seandepagnier/ais_monitor/src/nmea.py

#   Copyright (C) 2024 Sean D'Epagnier
#
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
# nmea uses a simple xor checksum
def nmea_cksum(msg):
    value = 0
    for c in msg: # skip over the $ at the begining of the sentence
        value ^= ord(c)
    return value & 255

def check_nmea_cksum(line):
    cksplit = line.split('*')
    try:
        computed = nmea_cksum(cksplit[0][1:])
        lineck = int(cksplit[1], 16)
        if computed == lineck:
            return True
        print('chekcsum faild', computed, lineck)
        return False
    except Exception as e:
        print('failed checksum exception', e)
        return False
