seandepagnier/ais_monitor/src/non_blocking_readline.py

#   Copyright (C) 2024 Sean D'Epagnier
#
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

buffers = {}

def non_blocking_readline(uart):
    if not uart in buffers:
        buffers[uart] = bytearray()

    line_buffer = buffers[uart]

    line = uart.readline()  # Attempt to read a line (non-blocking)
    if line:
        line_buffer.extend(line)
        if line.endswith(b'\n'):  # Check if the line is complete
            complete_line = line_buffer
            buffers[uart] = bytearray()  # Clear the buffer for the next line
            return complete_line.decode()
    return None  # Return None if no complete line was available
